tuptus922-tech/esp32-robot/cad_models/podglad_dreadnought_front.png

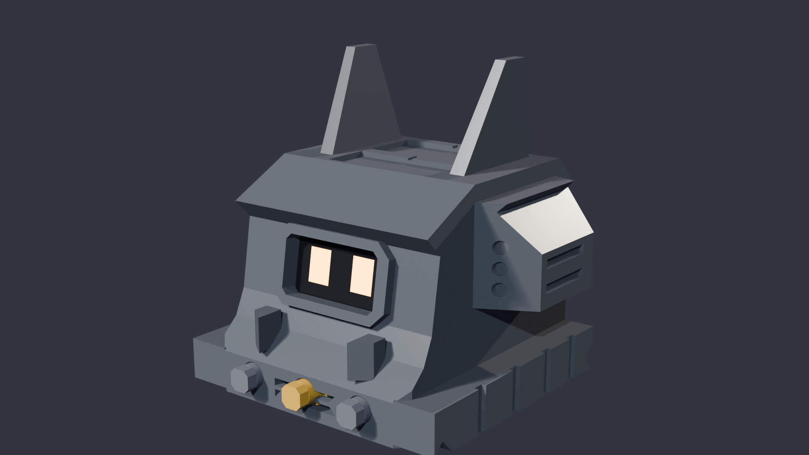
cad_models/podglad_dreadnought_front.png
