tuptus922-tech/esp32-robot/cad_models/podglad_dreadnought_tyl.png

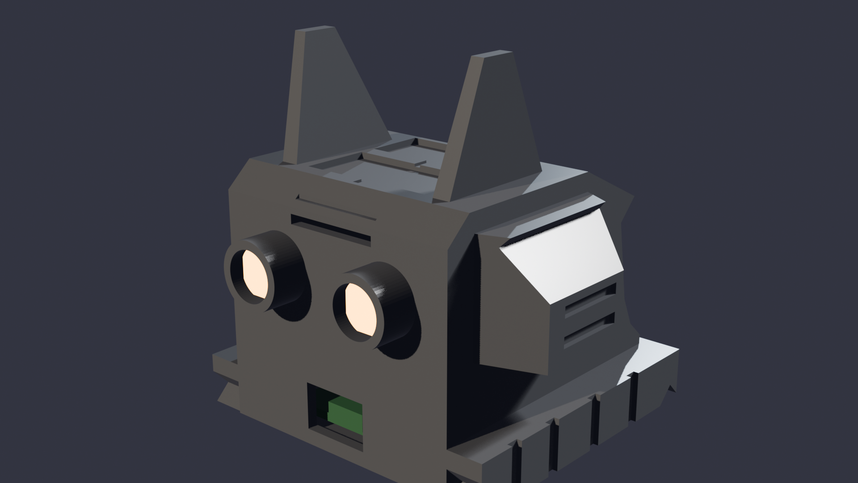
cad_models/podglad_dreadnought_tyl.png
