tuptus922-tech/esp32-robot/cad_models/podglad_kawaii_front.png

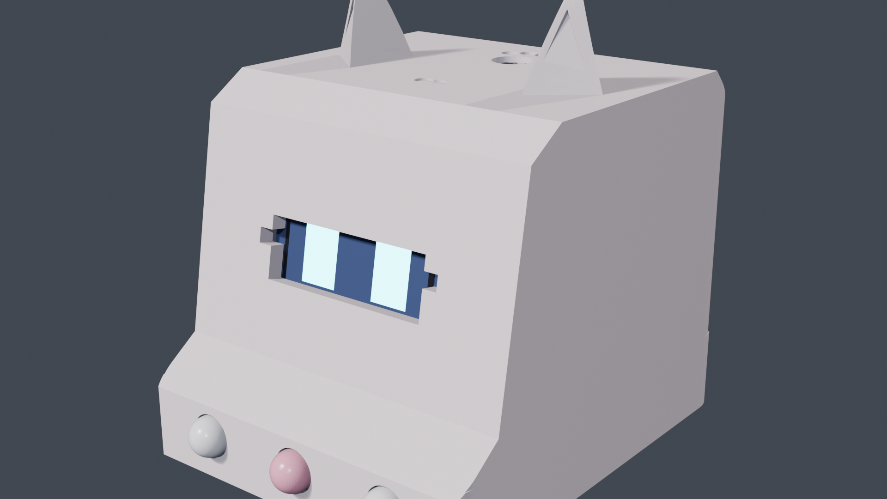
cad_models/podglad_kawaii_front.png
