tuptus922-tech/esp32-robot/cad_models/podglad_mecha_kawaii_szpontery.png

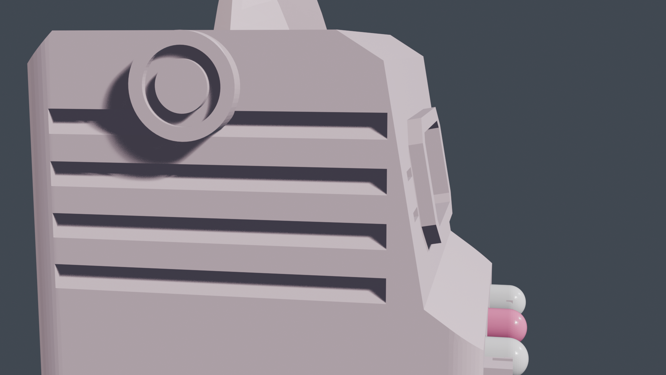
cad_models/podglad_mecha_kawaii_szpontery.png
