tuptus922-tech/esp32-robot/cad_models/stl_print/dieselpunk/components/nautilus_kominy.stl

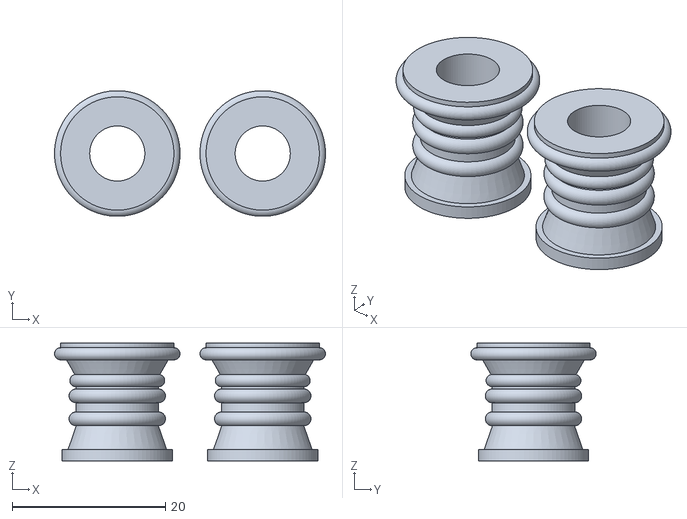
[picture p29: CAD file, 2026-09-13]
cad_models/stl_print/dieselpunk/components/nautilus_kominy.stl
35.4 x 16.4 x 15.4
