tuptus922-tech/esp32-robot/cad_models/stl_print/dieselpunk/dieselpunk_robot_kompletny.stl

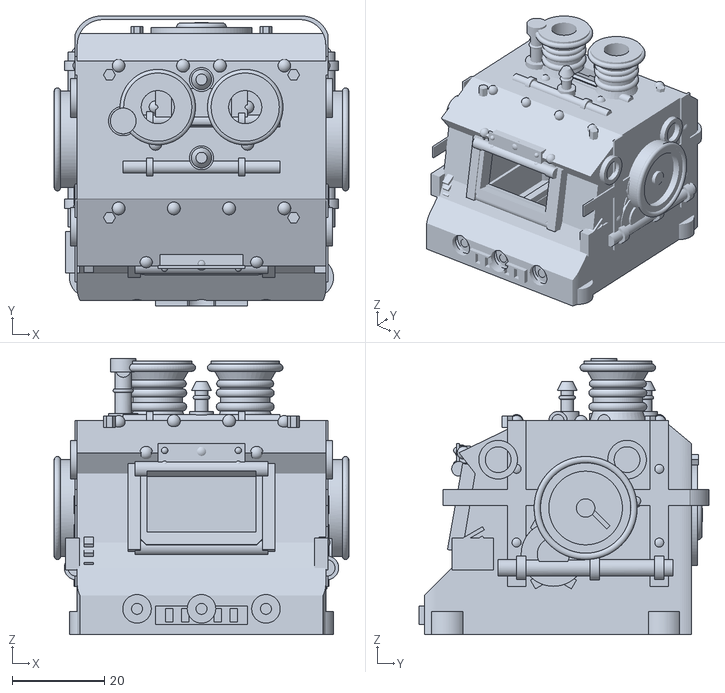
[picture p30: CAD file, 2026-09-13]
cad_models/stl_print/dieselpunk/dieselpunk_robot_kompletny.stl
64.0 x 63.0 x 60.0
