tuptus922-tech/esp32-robot/cad_models/stl_print/kawaii/kawaii_robot_kompletny.stl

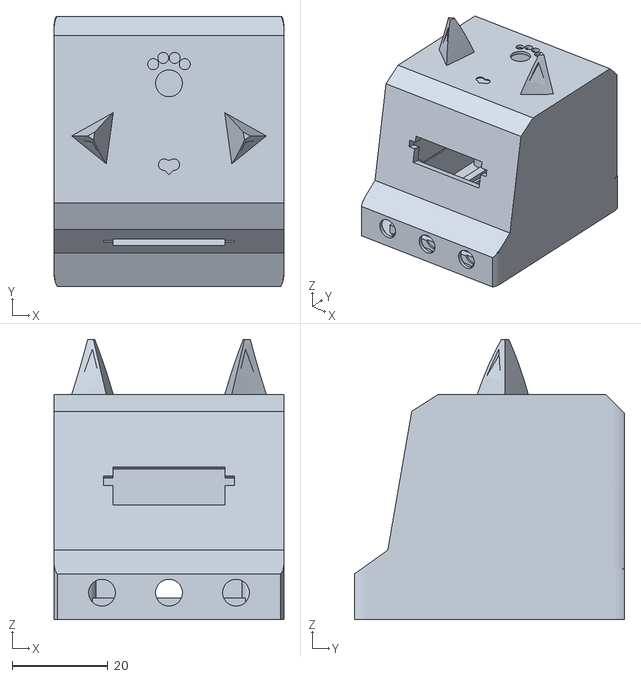
[picture p31: CAD file, 2026-09-12]
cad_models/stl_print/kawaii/kawaii_robot_kompletny.stl
48.0 x 56.5 x 58.5
