tuptus922-tech/esp32-robot/cad_models/stl_print/mecha_kawaii/mecha_kawaii_robot_kompletny.stl

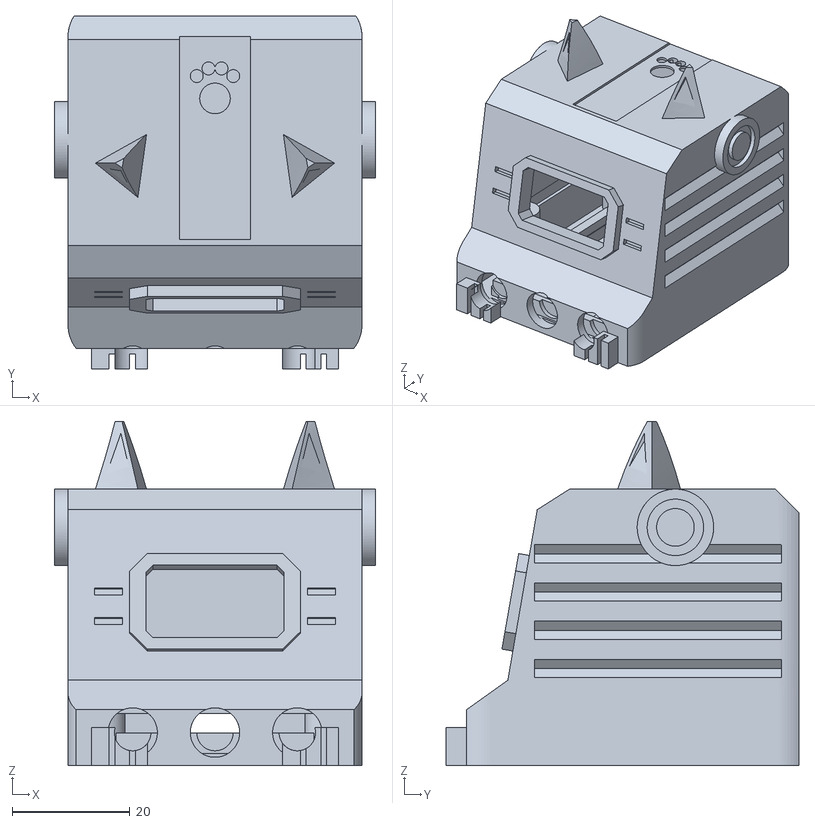
[picture p32: CAD file, 2026-09-13]
cad_models/stl_print/mecha_kawaii/mecha_kawaii_robot_kompletny.stl
54.6 x 60.0 x 58.5
