tuptus922-tech/esp32-robot/cad_models/stl_print/dieselpunk/components/nautilus_rurociagi.stl

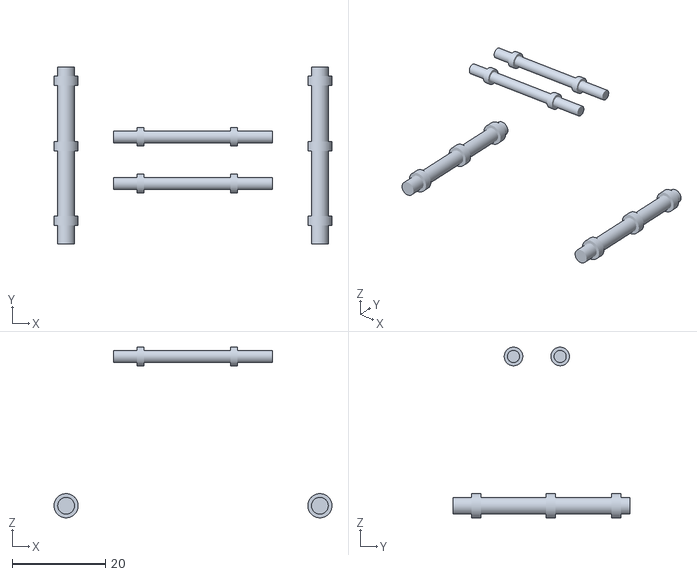
[picture p33: CAD file, 2026-09-13]
cad_models/stl_print/dieselpunk/components/nautilus_rurociagi.stl
59.6 x 38.0 x 36.6
