tuptus922-tech/esp32-robot/cad_models/stl_print/dieselpunk/dieselpunk_przycisk_zawor.stl

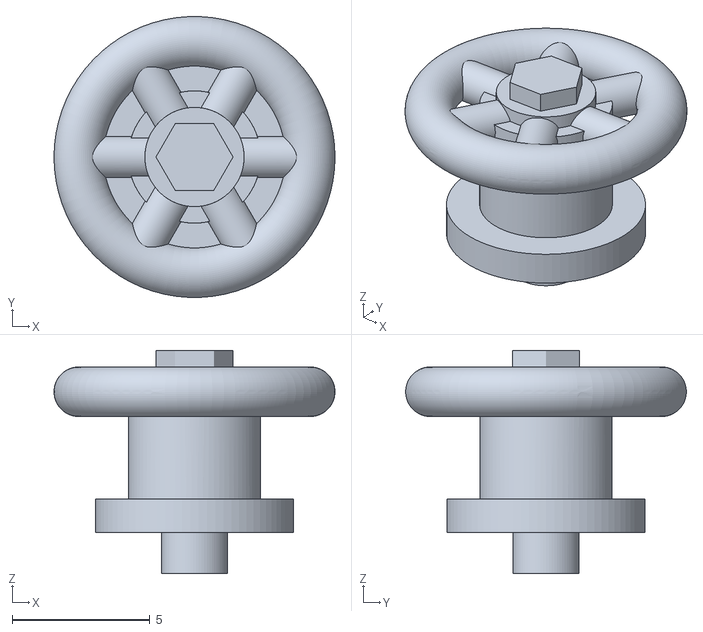
[picture p34: CAD file, 2026-09-13]
cad_models/stl_print/dieselpunk/dieselpunk_przycisk_zawor.stl
10.2 x 10.2 x 8.10
