tuptus922-tech/esp32-robot/cad_models/stl_print/dreadnought/dreadnought_podstawa.stl

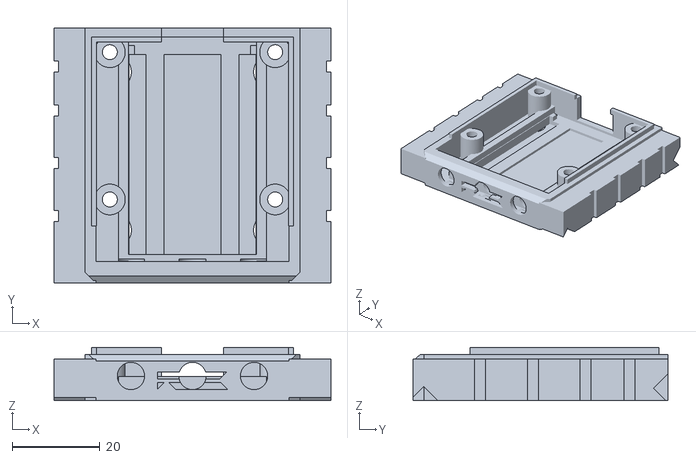
[picture p35: CAD file, 2026-09-13]
cad_models/stl_print/dreadnought/dreadnought_podstawa.stl
63.0 x 58.0 x 12.1
