tuptus922-tech/esp32-robot/cad_models/stl_print/kawaii/kawaii_przycisk_lapka.stl

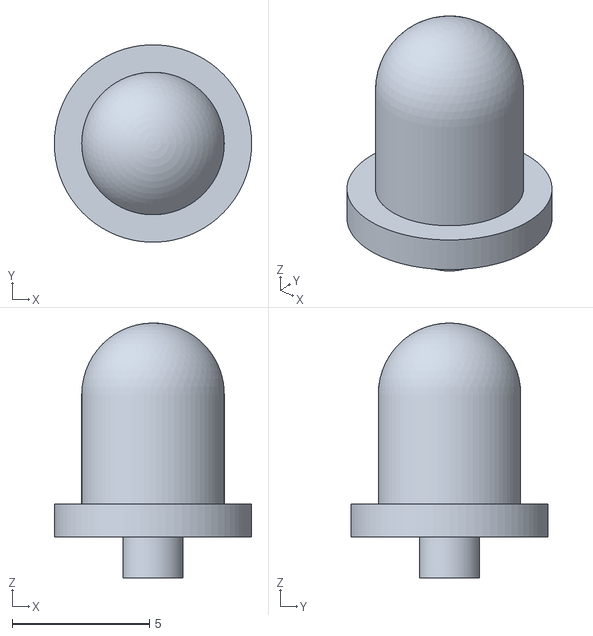
[picture p36: CAD file, 2026-09-12]
cad_models/stl_print/kawaii/kawaii_przycisk_lapka.stl
7.20 x 7.19 x 9.30
