tuptus922-tech/esp32-robot/cad_models/blender_models/MPU6050_Ruch.stl

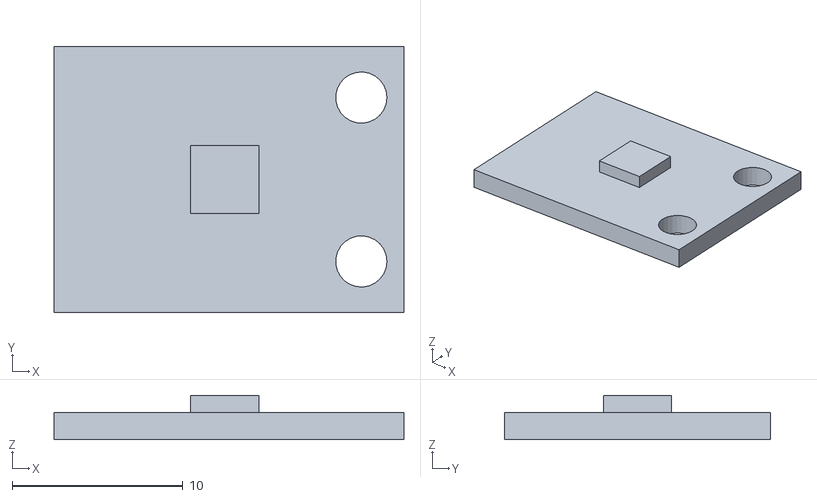
[picture p37: CAD file, 2026-09-12]
cad_models/blender_models/MPU6050_Ruch.stl
20.5 x 15.6 x 2.60
