tuptus922-tech/esp32-robot/cad_models/stl_print/dieselpunk/components/nautilus_iluminatory.stl

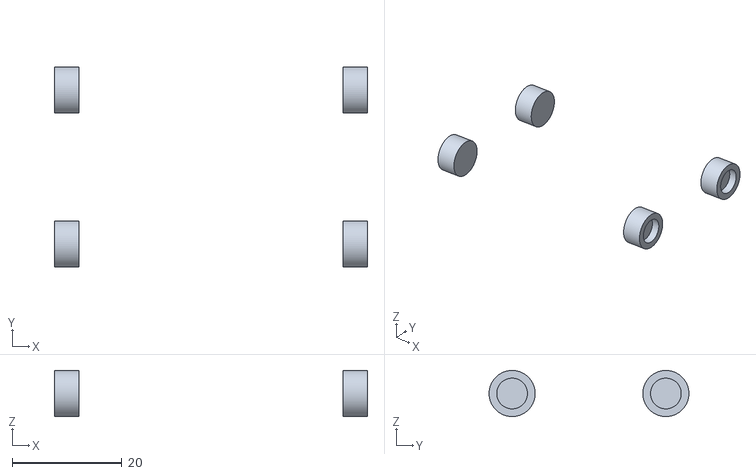
[picture p38: CAD file, 2026-09-13]
cad_models/stl_print/dieselpunk/components/nautilus_iluminatory.stl
57.0 x 36.4 x 8.40
