tuptus922-tech/esp32-robot/cad_models/stl_print/dreadnought/dreadnought_robot_kompletny.stl

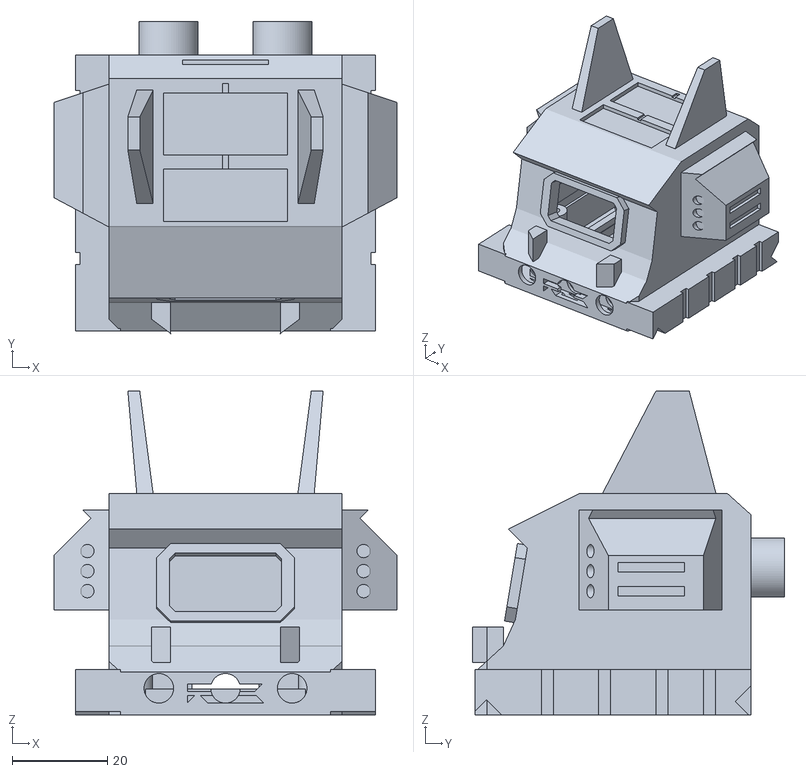
[picture p39: CAD file, 2026-09-13]
cad_models/stl_print/dreadnought/dreadnought_robot_kompletny.stl
72.0 x 65.5 x 68.0
