tuptus922-tech/esp32-robot/cad_models/stl_print/mecha_kawaii/mecha_kawaii_glowa.stl

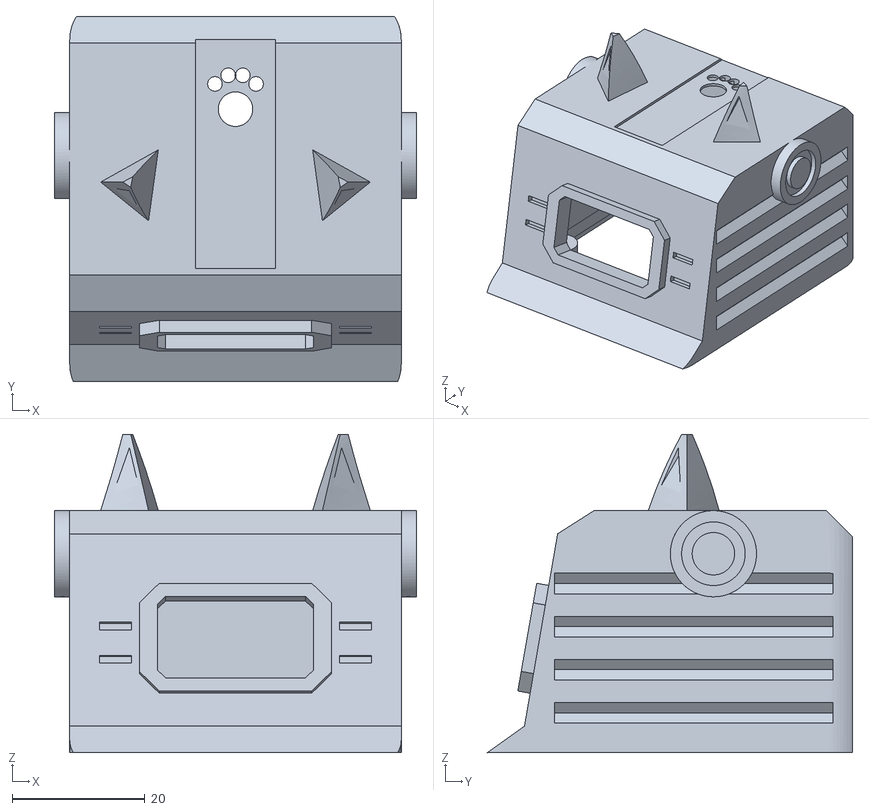
[picture p40: CAD file, 2026-09-12]
cad_models/stl_print/mecha_kawaii/mecha_kawaii_glowa.stl
54.6 x 55.1 x 48.0
