tuptus922-tech/esp32-robot/cad_models/blender_models/Buzzer.stl

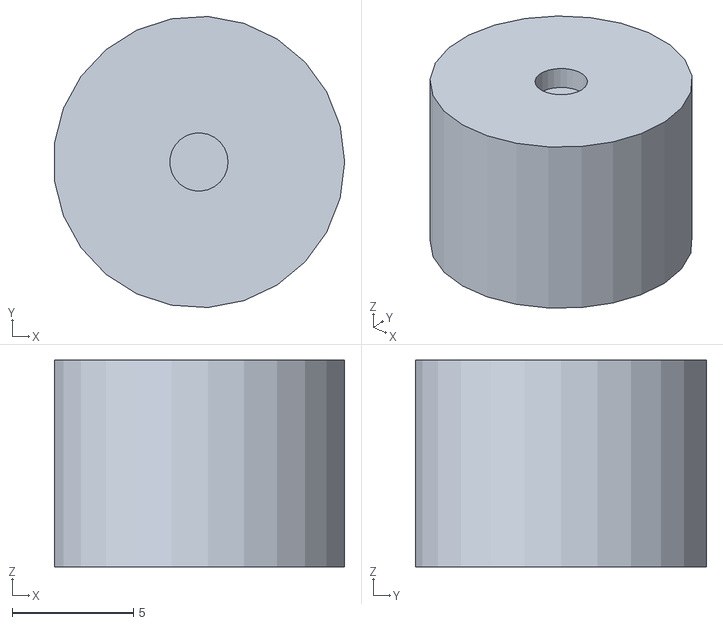
[picture p41: CAD file, 2026-09-12]
cad_models/blender_models/Buzzer.stl
12.0 x 12.0 x 8.50
