tuptus922-tech/esp32-robot/cad_models/robot_dreadnought_3d.FCStd

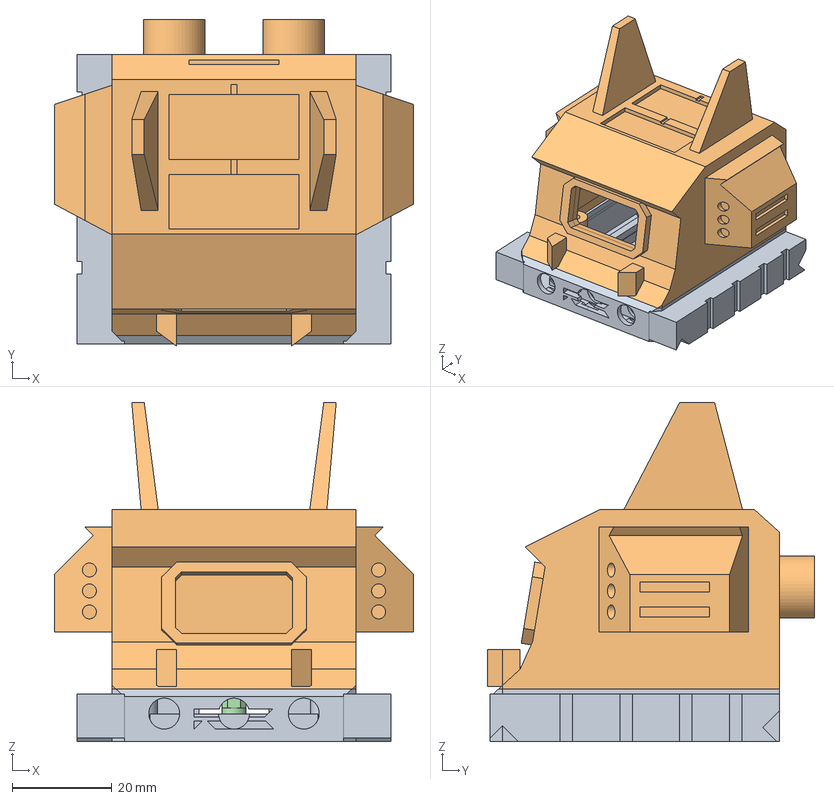
[picture p42: CAD file, 2026-09-13]
cad_models/robot_dreadnought_3d.FCStd
72.0 x 65.5 x 68.0 mm
Dreadnought_Podstawa
Dreadnought_Glowa
Dreadnought_Przycisk_Romb
Dreadnought_Przycisk_Strzalka_L
Dreadnought_Przycisk_Strzalka_P
