tuptus922-tech/esp32-robot/cad_models/stl_print/dieselpunk/components/nautilus_klatka_okna.stl

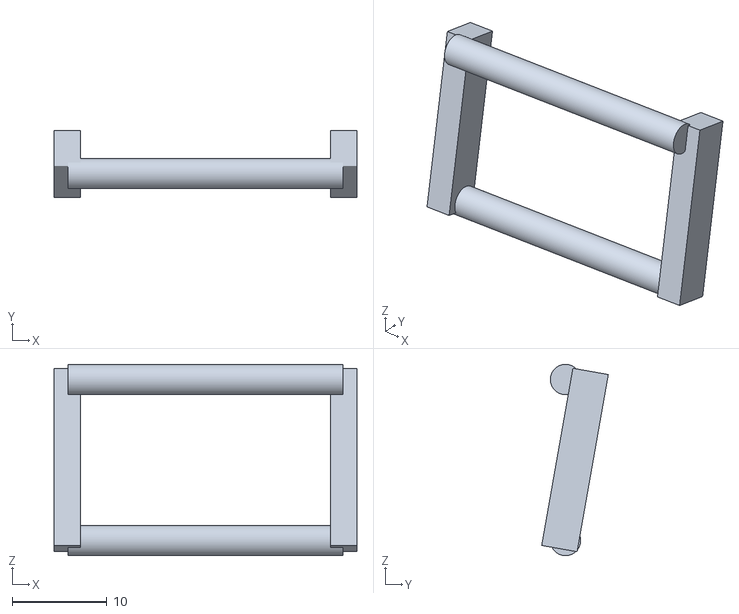
[picture p43: CAD file, 2026-09-13]
cad_models/stl_print/dieselpunk/components/nautilus_klatka_okna.stl
32.0 x 7.04 x 20.2
