tuptus922-tech/esp32-robot/cad_models/stl_print/dieselpunk/dieselpunk_glowa.stl

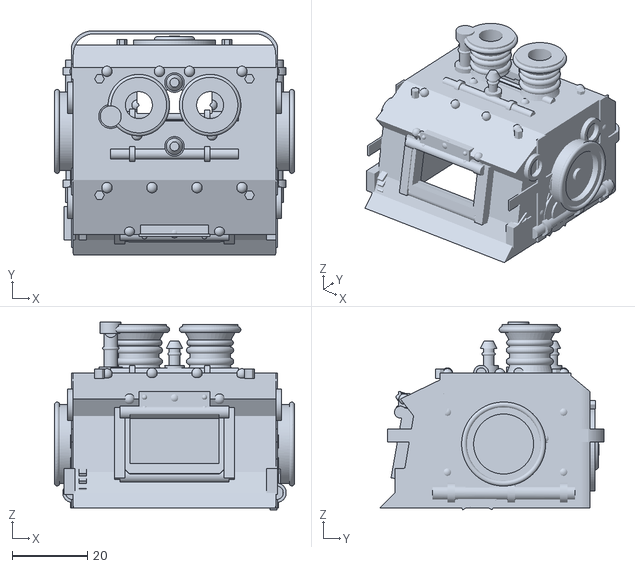
[picture p44: CAD file, 2026-09-13]
cad_models/stl_print/dieselpunk/dieselpunk_glowa.stl
64.0 x 59.8 x 50.1
