tuptus922-tech/esp32-robot/cad_models/stl_print/dreadnought/dreadnought_glowa.stl

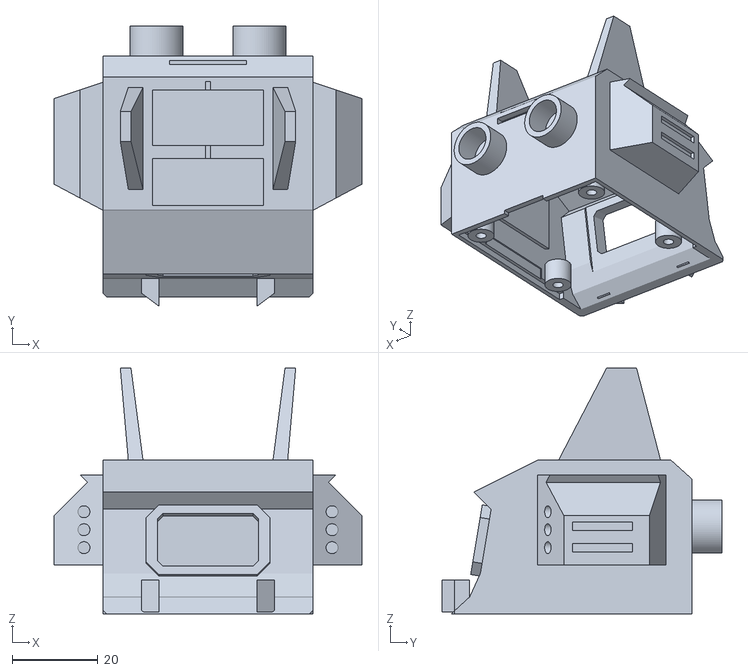
[picture p45: CAD file, 2026-09-12]
cad_models/stl_print/dreadnought/dreadnought_glowa.stl
72.0 x 65.5 x 57.5
