tuptus922-tech/esp32-robot/cad_models/blender_models/robot_caly_szkielet.stl

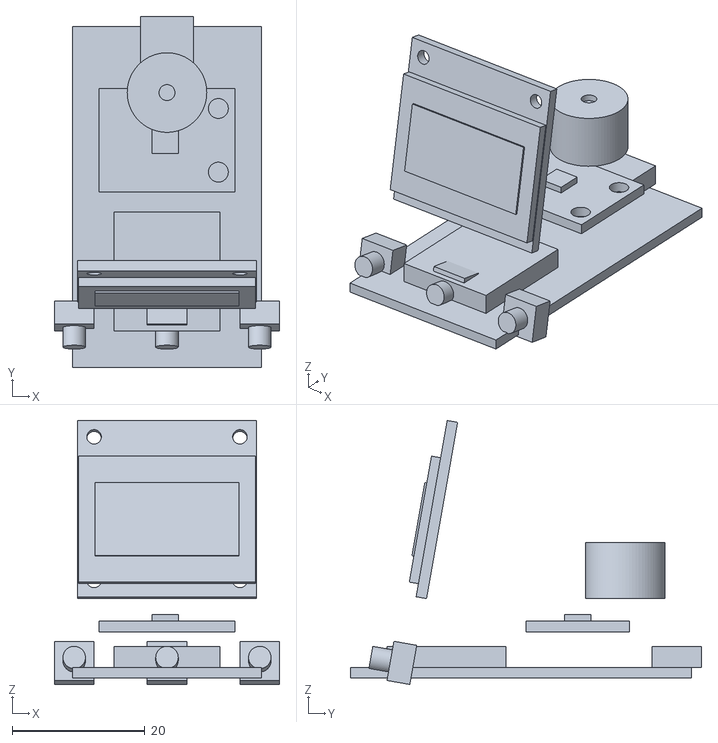
[picture p46: CAD file, 2026-09-12]
cad_models/blender_models/robot_caly_szkielet.stl
34.0 x 53.0 x 39.8
