tuptus922-tech/esp32-robot/cad_models/robot_mecha_kawaii_3d.FCStd

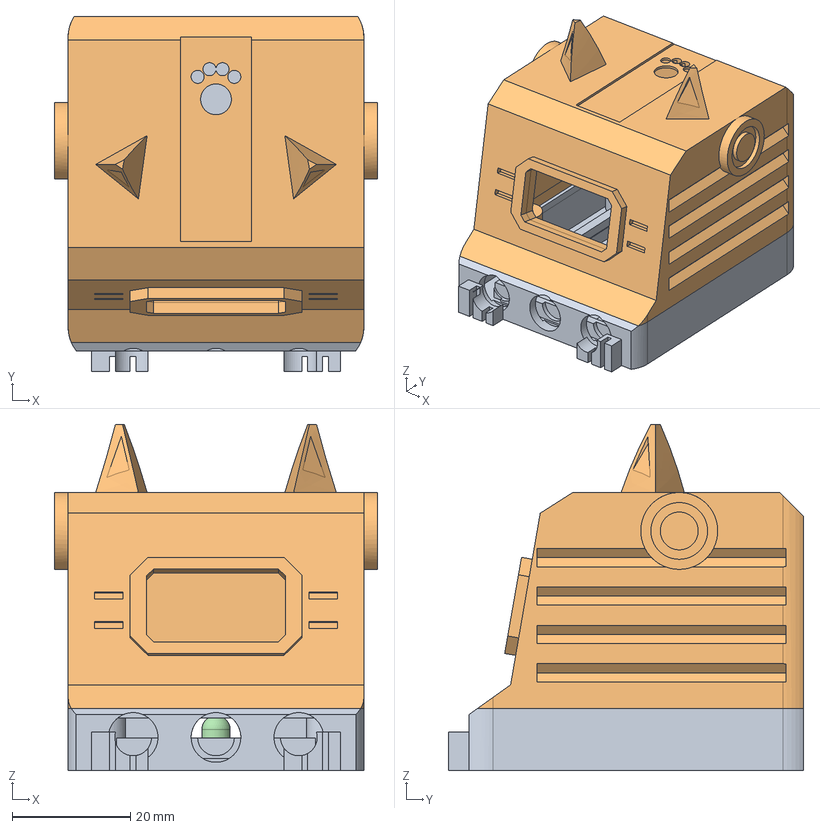
[picture p47: CAD file, 2026-09-13]
cad_models/robot_mecha_kawaii_3d.FCStd
54.6 x 60.0 x 58.5 mm
Mecha_Kawaii_Podstawa
Mecha_Kawaii_Glowa
Mecha_Kawaii_Przycisk_Serce
Mecha_Kawaii_Przycisk_Lapka
