tuptus922-tech/esp32-robot/cad_models/robot_obudowa_3d.FCStd

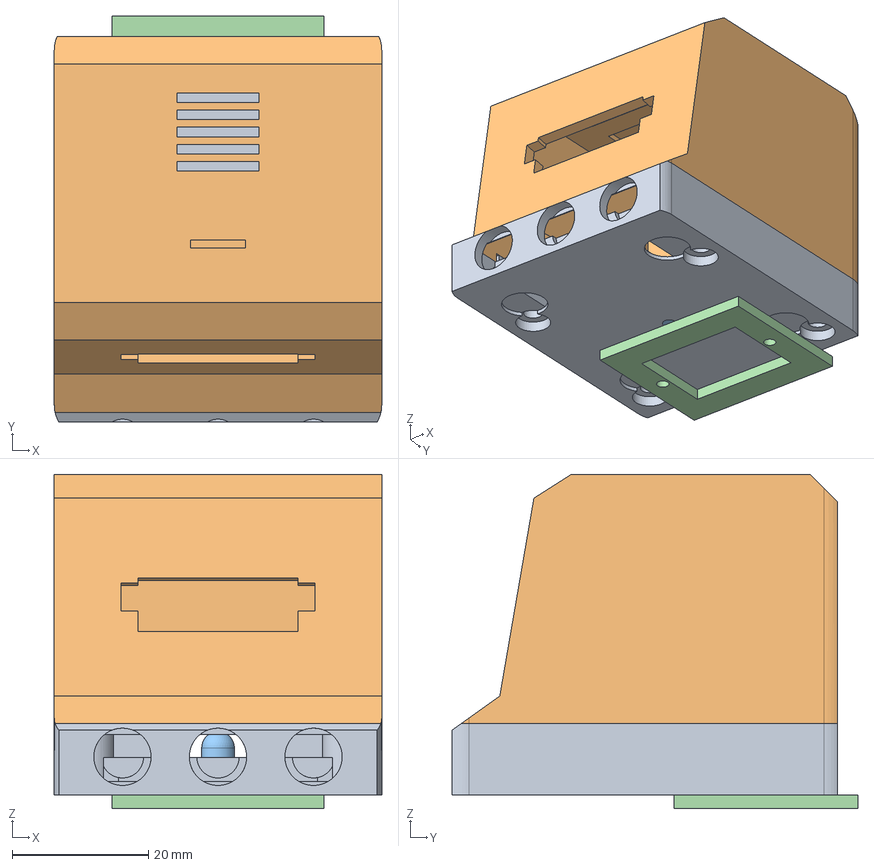
[picture p48: CAD file, 2026-09-13]
cad_models/robot_obudowa_3d.FCStd
48.0 x 59.5 x 49.0 mm
Obudowa_Dol_Podstawa
Obudowa_Gora_Glowa
Przycisk_Nakladka
Uchwyt_OLED
