tuptus922-tech/esp32-robot/cad_models/robot_dieselpunk_3d.FCStd

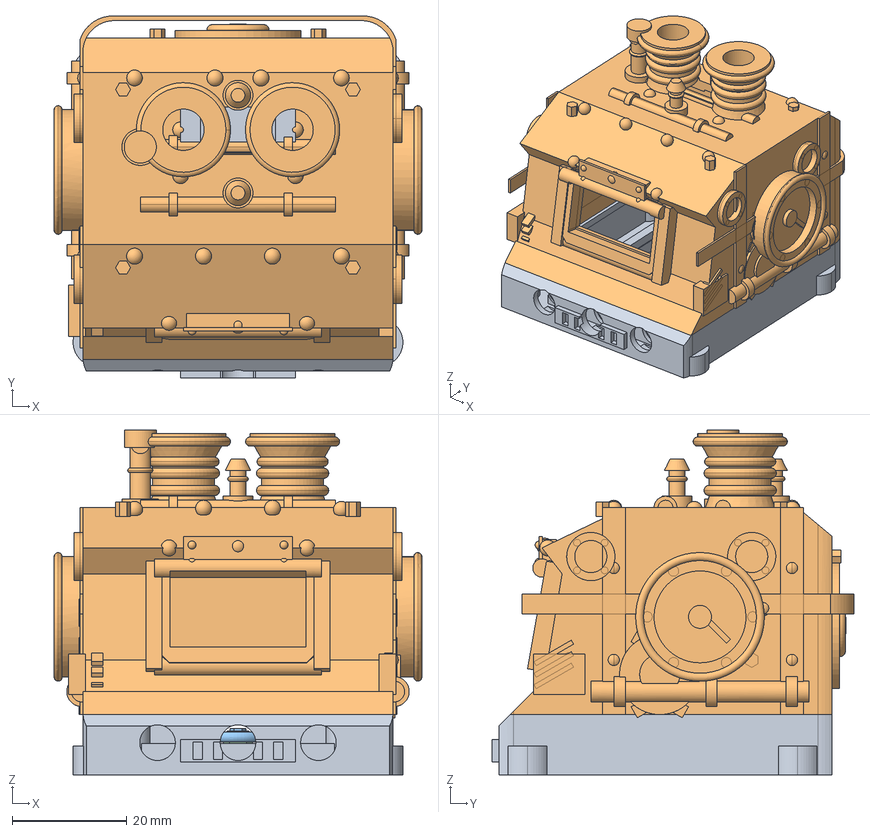
[picture p49: CAD file, 2026-09-13]
cad_models/robot_dieselpunk_3d.FCStd
64.0 x 63.0 x 60.0 mm
Nautilus_Podstawa
Nautilus_Glowa
Nautilus_Przycisk_Zawor
Nautilus_Przycisk_Ryfel_L
Nautilus_Przycisk_Ryfel_P
