tuptus922-tech/esp32-robot/cad_models/robot_kawaii_3d.FCStd

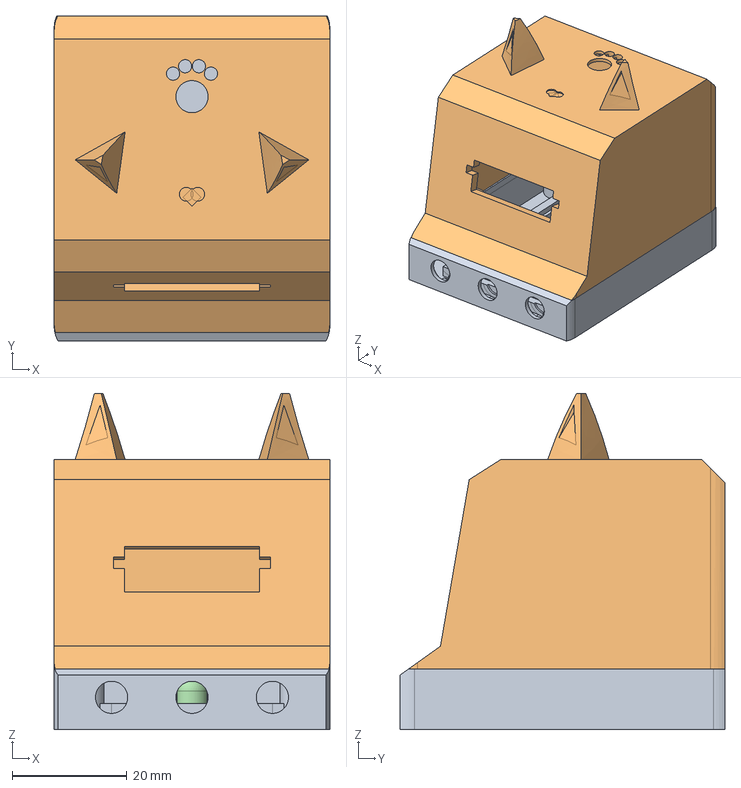
[picture p50: CAD file, 2026-09-12]
cad_models/robot_kawaii_3d.FCStd
48.0 x 56.5 x 58.5 mm
Obudowa_Dol_Podstawa
Kawaii_Obudowa_Gora_Glowa
Kawaii_Przycisk_Serce
Kawaii_Przycisk_Lapka
