tuptus922-tech/esp32-robot/cad_models/oled_0_96_ssd1306.step

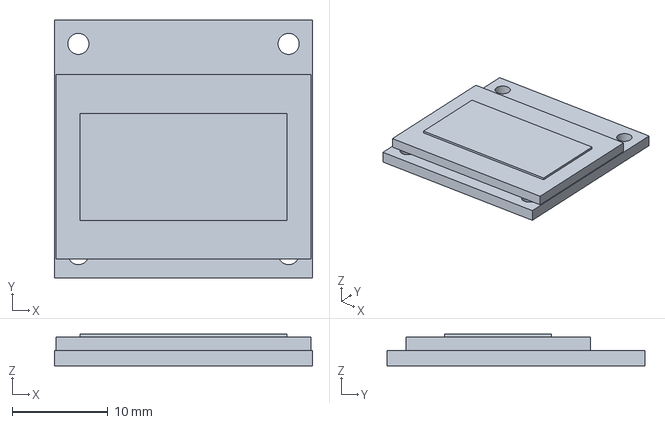
[picture p51: CAD file, 2026-09-12]
cad_models/oled_0_96_ssd1306.step
27.0 x 27.0 x 3.30 mm
