tuptus922-tech/esp32-robot/cad_models/robot_uklad_3d.FCStd

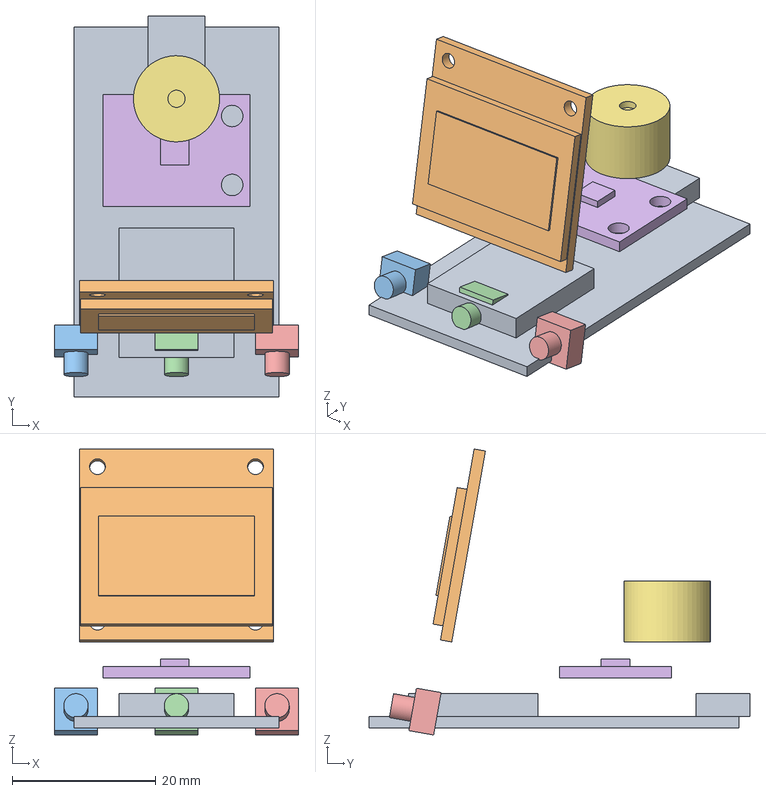
[picture p52: CAD file, 2026-09-12]
cad_models/robot_uklad_3d.FCStd
34.0 x 53.0 x 39.8 mm
ESP32_Podstawa
OLED_Twarz
Przycisk_Lewo
Przycisk_OK
Przycisk_Prawo
MPU6050_Ruch
Buzzer
