tuptus922-tech/esp32-robot/cad_models/tact_switch_6x6.step

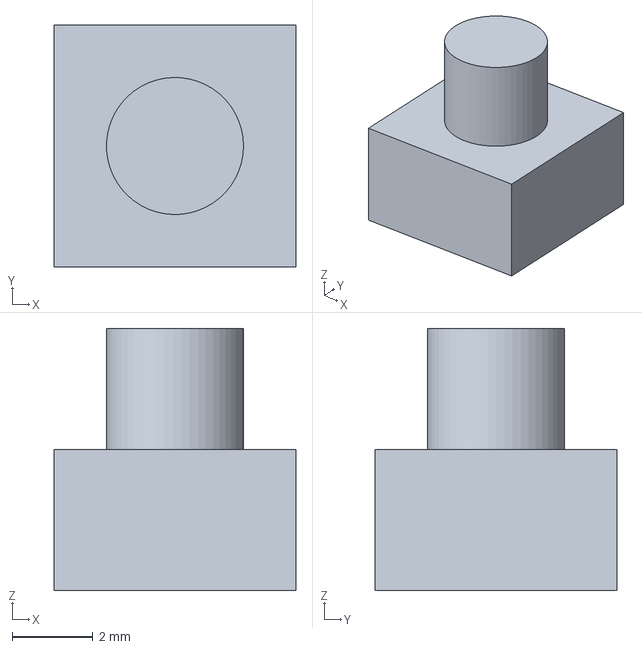
[picture p53: CAD file, 2026-09-12]
cad_models/tact_switch_6x6.step
6.00 x 6.00 x 6.50 mm
