tuptus922-tech/esp32-robot/cad_models/robot_podzespoly.FCStd

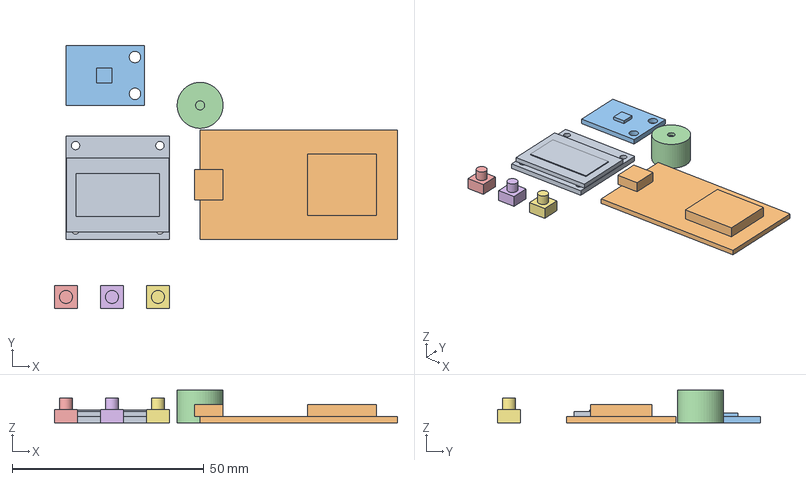
[picture p54: CAD file, 2026-09-12]
cad_models/robot_podzespoly.FCStd
89.5 x 68.6 x 8.50 mm
OLED_0_96_SSD1306
ESP32_DevKit_V1
MPU6050_GY521
Buzzer_12mm
Przycisk_Lewo
Przycisk_OK
Przycisk_Prawo
